mvendert/ESP32Shutter/ESP32Shutter/include/Ky008LaserSensor.h

#pragma once

#include <Arduino.h>

class Ky008LaserSensor {
 public:
  explicit Ky008LaserSensor(uint8_t pin, uint8_t inputMode = INPUT,
                            bool beamDetectedState = HIGH);

  void begin();
  bool isBeamDetected() const;
  bool isBeamBroken() const;
  int readRaw() const;

 private:
  uint8_t pin_;
  uint8_t inputMode_;
  bool beamDetectedState_;
};
